anoosantoos-creator/PC-Fan-Airflow-Guide/results/solver_residual_summary.csv

case | iterations | last_initial_residual_ux | last_initial_residual_uy | last_initial_residual_uz | last_initial_residual_p | last_initial_residual_k | last_initial_residual_omega | last_global_continuity_error | status
baseline_no_guide | 800 | 0.00041520658 | 0.0049287822 | 0.0045762391 | 0.00018008135 | 0.00076967204 | 0.00031975862 | 5.5722683e-07 | Maximum iteration count reached before all residual controls
design_A_low_blockage | 800 | 0.00033967786 | 0.0035759514 | 0.0032296429 | 0.00010447697 | 0.00079596478 | 0.00039685762 | -1.8438271e-06 | Maximum iteration count reached before all residual controls
design_B_angled_guide | 800 | 0.00036557005 | 0.0039712906 | 0.004289439 | 0.00012979401 | 0.00069908838 | 0.00033516511 | -4.6058993e-07 | Maximum iteration count reached before all residual controls
design_C_balanced_revision | 800 | 0.0003026183 | 0.0032766289 | 0.0028865056 | 7.137326e-05 | 0.00082862773 | 0.00033008003 | 8.0290415e-07 | Maximum iteration count reached before all residual controls
