anoosantoos-creator/PC-Fan-Airflow-Guide/results/figures/velocity_magnitude_x100.png

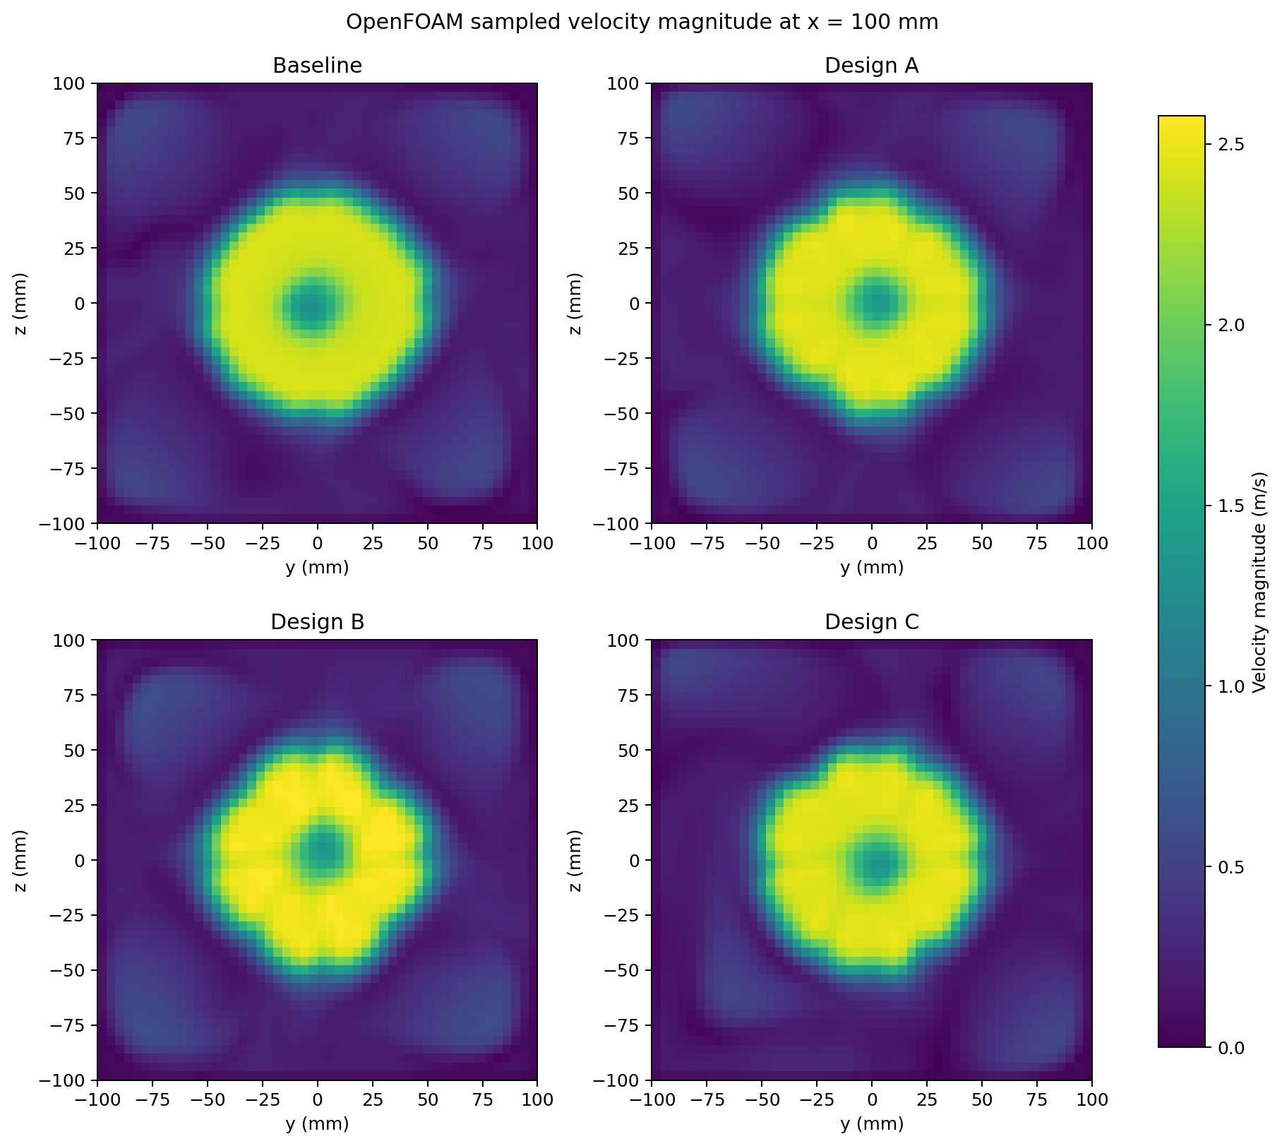
results/figures/velocity_magnitude_x100.png
